urjaman/dasholedsw/mfont8x8.c

#include <stdint.h>
#include <avr/pgmspace.h>

const uint8_t PROGMEM my_font[224][8] = {
	{ 0x00, 0x00, 0x00, 0x00, 0x00, 0x00, 0x00, 0x00 },
	{ 0x00, 0x00, 0x00, 0x7A, 0x00, 0x00, 0x00, 0x00 },
	{ 0x00, 0x00, 0x60, 0x00, 0x00, 0x60, 0x00, 0x00 },
	{ 0x00, 0x24, 0x7E, 0x24, 0x24, 0x7E, 0x24, 0x00 },
	{ 0x00, 0x00, 0x3A, 0x2A, 0x7F, 0x2A, 0x2E, 0x00 },
	{ 0x00, 0x62, 0x64, 0x08, 0x10, 0x26, 0x46, 0x00 },
	{ 0x00, 0x04, 0x2A, 0x52, 0x2A, 0x04, 0x0A, 0x00 },
	{ 0x00, 0x00, 0x00, 0x00, 0x60, 0x00, 0x00, 0x00 },
	{ 0x00, 0x00, 0x00, 0x00, 0x3C, 0x42, 0x00, 0x00 },
	{ 0x00, 0x00, 0x42, 0x3C, 0x00, 0x00, 0x00, 0x00 },
	{ 0x00, 0x00, 0x08, 0x2A, 0x1C, 0x2A, 0x08, 0x00 },
	{ 0x00, 0x00, 0x08, 0x08, 0x3E, 0x08, 0x08, 0x00 },
	{ 0x00, 0x00, 0x00, 0x01, 0x06, 0x00, 0x00, 0x00 },
	{ 0x00, 0x00, 0x08, 0x08, 0x08, 0x08, 0x08, 0x00 },
	{ 0x00, 0x00, 0x00, 0x06, 0x06, 0x00, 0x00, 0x00 },
	{ 0x00, 0x00, 0x02, 0x04, 0x08, 0x10, 0x20, 0x00 },
	{ 0x00, 0x3C, 0x46, 0x4A, 0x52, 0x62, 0x3C, 0x00 },
	{ 0x00, 0x00, 0x22, 0x42, 0x7E, 0x02, 0x02, 0x00 },
	{ 0x00, 0x26, 0x4A, 0x4A, 0x4A, 0x4A, 0x32, 0x00 },
	{ 0x00, 0x24, 0x42, 0x42, 0x52, 0x52, 0x2C, 0x00 },
	{ 0x00, 0x0C, 0x14, 0x24, 0x7E, 0x04, 0x04, 0x00 },
	{ 0x00, 0x74, 0x52, 0x52, 0x52, 0x52, 0x4C, 0x00 },
	{ 0x00, 0x3C, 0x52, 0x52, 0x52, 0x52, 0x0C, 0x00 },
	{ 0x00, 0x40, 0x40, 0x46, 0x48, 0x50, 0x60, 0x00 },
	{ 0x00, 0x2C, 0x52, 0x52, 0x52, 0x52, 0x2C, 0x00 },
	{ 0x00, 0x30, 0x4A, 0x4A, 0x4A, 0x4A, 0x3C, 0x00 },
	{ 0x00, 0x00, 0x00, 0x12, 0x00, 0x00, 0x00, 0x00 },
	{ 0x00, 0x00, 0x01, 0x26, 0x00, 0x00, 0x00, 0x00 },
	{ 0x00, 0x00, 0x00, 0x08, 0x14, 0x22, 0x00, 0x00 },
	{ 0x00, 0x00, 0x14, 0x14, 0x14, 0x14, 0x14, 0x00 },
	{ 0x00, 0x00, 0x00, 0x22, 0x14, 0x08, 0x00, 0x00 },
	{ 0x00, 0x20, 0x40, 0x40, 0x4A, 0x50, 0x20, 0x00 },
	{ 0x00, 0x3C, 0x42, 0x5A, 0x6A, 0x5A, 0x38, 0x00 },
	{ 0x00, 0x3E, 0x48, 0x48, 0x48, 0x48, 0x3E, 0x00 },
	{ 0x00, 0x7E, 0x52, 0x52, 0x52, 0x52, 0x2C, 0x00 },
	{ 0x00, 0x3C, 0x42, 0x42, 0x42, 0x42, 0x24, 0x00 },
	{ 0x00, 0x7E, 0x42, 0x42, 0x42, 0x24, 0x18, 0x00 },
	{ 0x00, 0x7E, 0x52, 0x52, 0x52, 0x52, 0x42, 0x00 },
	{ 0x00, 0x7E, 0x50, 0x50, 0x50, 0x50, 0x40, 0x00 },
	{ 0x00, 0x3C, 0x42, 0x42, 0x4A, 0x4A, 0x2C, 0x00 },
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
};
