urjaman/dasholedsw/lcd.c

#include "main.h"
#include <stdbool.h>
#include <stdint.h>
#include <stdio.h>
#include <avr/io.h>
#include <util/delay.h>

#include "lcd.h"

static uint8_t lcdx, lcdy;

void
lcd_init(void)
{
	dp_init();
}

void lcd_gotoxy(uint8_t x, uint8_t y)
{
	if (y>=LCD_MAXY) y=0;
	if (x>=LCD_MAXX) x=0;
	lcdy = y;
	lcdx = (x*8);
}

void lcd_gotoxy_dw(uint8_t x, uint8_t y)
{
	if (y>=LCD_MAXY) y=0;
	if (x>=LCD_DW_MAXX) x=0;
	lcdy = y;
	lcdx = x;
}


void lcd_clear(void)
{
	dp_clear_block(0, 0, LCDWIDTH, LCDHEIGHT/8);
}

static void lcd_clear_dw_dh(uint8_t w, uint8_t h)
{
	if ((lcdx+w)>LCDWIDTH) {
		w = LCDWIDTH - lcdx;
	}
	dp_clear_block(lcdx, lcdy, w, h);
	lcdx += w;
}

void lcd_clear_dw(uint8_t w)
{
	lcd_clear_dw_dh(w, 1);
}

void lcd_clear_big_dw(uint8_t w)
{
	lcd_clear_dw_dh(w, 2);
}

void lcd_clear_dbig_dw(uint8_t w)
{
	lcd_clear_dw_dh(w, 4);
}

static void lcd_clear_eol_dh(uint8_t h)
{
	dp_clear_block(lcdx, lcdy, LCDWIDTH - lcdx, h);
	lcdx = 0;
	lcdy += h;
}

void lcd_clear_eol(void)
{
	lcd_clear_eol_dh(1);
}

void lcd_clear_big_eol(void)
{
	lcd_clear_eol_dh(2);
}

void lcd_clear_dbig_eol(void)
{
	lcd_clear_eol_dh(4);
}

void lcd_clear_eos(void)
{
	while (lcdy < LCD_MAXY) lcd_clear_eol();
	lcdy = 0;
}

void lcd_write_dwb(uint8_t *buf, uint8_t w)
{
	if ((lcdx+w)>LCDWIDTH) {
		w = LCDWIDTH - lcdx;
	}
	dp_write_block(buf, lcdx, lcdy, w, 1);
	lcdx += w;
}

#include "mfont8x8.c"

// Some data for dynamic width mode with this font.
#include "font-dyn-meta.c"

static PGM_P get_block(uint8_t *w, unsigned char c, uint8_t dw)
{
	PGM_P block;
	if (c < 0x20) c = 0x20;
	block = (const char*)&(my_font[c-0x20][0]);
	*w = 8;
	if (dw) {
		uint8_t font_meta_b = pgm_read_byte(&(font_metadata[c-0x20]));
		block += XOFF(font_meta_b);
		*w = DW(font_meta_b);
	}
	return block;
}

uint8_t lcd_get_strbuf(uint8_t *b, const unsigned char*str, uint8_t dw)
{
	uint8_t o=0,w;
	PGM_P block;
	while (*str) {
		block = get_block(&w, *str++, dw);
		memcpy_P(b+o, block, w);
		o += w;
	}
	return o;
}

static void lcd_putchar_(unsigned char c, uint8_t dw)
{

	uint8_t w;
	PGM_P block = get_block(&w, c, dw);
	if ((lcdx+w)>LCDWIDTH) {
		w = LCDWIDTH - lcdx;
	}
	dp_write_block_P(block, lcdx, lcdy, w, 1);
	lcdx += w;
}



static void lcd_putchar_big(unsigned char c)
{
	uint8_t buf[32];

	uint8_t w;
	PGM_P block = get_block(&w, c, 1);

	if ((lcdx+(w*2))>LCDWIDTH) {
		w = (LCDWIDTH - lcdx)/2;
	}
	for (int i=0; i<w; i++) {
		uint8_t d = pgm_read_byte(block);
		block++;
		uint8_t hi = 0;
		uint8_t lo = 0;
		for (int i=0; i<4; i++) {
			hi = hi >> 2;
			lo = lo >> 2;
			if (d & _BV(4+i)) hi |= 0xC0;
			if (d & _BV(i)) lo |= 0xC0;
		}
		buf[i*2] = hi;
		buf[i*2+1] = hi;
		buf[(w+i)*2] = lo;
		buf[(w+i)*2+1] = lo;
	}
	dp_write_block(buf, lcdx, lcdy, w*2, 2);
	lcdx += w*2;
}


static void lcd_putchar_dbig(unsigned char c)
{
	uint8_t buf[128];

	uint8_t w;
	PGM_P block = get_block(&w, c, 1);
	if ((lcdx+(w*4))>LCDWIDTH) {
		w = (LCDWIDTH - lcdx)/2;
	}
	for (uint8_t i=0; i<w; i++) {
		uint8_t dat = pgm_read_byte(block);
		block++;
		uint8_t a = 0;
		uint8_t b = 0;
		uint8_t c = 0;
		uint8_t d = 0;
		for (uint8_t n=0; n<2; n++) {
			a = a >> 4;
			b = b >> 4;
			c = c >> 4;
			d = d >> 4;
			if (dat & _BV(6+n)) a |= 0xF0;
			if (dat & _BV(4+n)) b |= 0xF0;
			if (dat & _BV(2+n)) c |= 0xF0;
			if (dat & _BV(n))   d |= 0xF0;
		}
		memset(buf+i*4, a, 4);
		memset(buf+(w+i)*4, b, 4);
		memset(buf+(2*w+i)*4, c, 4);
		memset(buf+(3*w+i)*4, d, 4);
	}
	dp_write_block(buf, lcdx, lcdy, w*4, 4);
	lcdx += w*4;
}

static uint8_t lcd_dw_charw(uint8_t c)
{
	if (c < 0x20) c = 0x20;
	uint8_t font_meta_b = pgm_read_byte(&(font_metadata[c-0x20]));
	return DW(font_meta_b);
}


uint8_t lcd_strwidth(const unsigned char * str)
{
	uint8_t w = 0;
	do {
		if (*str) w += lcd_dw_charw(*str);
		else return w;
		str++;
	} while(1);
}

uint8_t lcd_strwidth_P(PGM_P str)
{
	uint8_t w = 0;
	do {
		uint8_t c = pgm_read_byte(str);
		if (c) w += lcd_dw_charw(c);
		else return w;
		str++;
	} while(1);
}

/* big = 2x small, but dont tell the user ;) */
uint8_t lcd_strwidth_big(const unsigned char * str)
{
	return lcd_strwidth(str)*2;
}

uint8_t lcd_strwidth_big_P(PGM_P str)
{
	return lcd_strwidth_P(str)*2;
}

/* dbig = 4x small, but dont tell the user ;) */
uint8_t lcd_strwidth_dbig(const unsigned char * str)
{
	return lcd_strwidth(str)*4;
}

uint8_t lcd_strwidth_dbig_P(PGM_P str)
{
	return lcd_strwidth_P(str)*4;
}

void lcd_putchar(unsigned char c)
{
	lcd_putchar_(c,0);
}

void lcd_puts(const unsigned char * str)
{
	do {
		if (*str) lcd_putchar_(*str, 0);
		else return;
		str++;
	} while(1);
}

void lcd_puts_P(PGM_P str)
{
	do {
		uint8_t c = pgm_read_byte(str);
		if (c) lcd_putchar_(c, 0);
		else return;
		str++;
	} while (1);
}

void lcd_puts_dw(const unsigned char * str)
{
start:
	if (*str) lcd_putchar_(*str, 1);
	else return;
	str++;
	goto start;
}

void lcd_puts_dw_P(PGM_P str)
{
	unsigned char c;
start:
	c = pgm_read_byte(str);
	if (c) lcd_putchar_(c, 1);
	else return;
	str++;
	goto start;
}


void lcd_puts_big_P(PGM_P str)
{
	unsigned char c;
start:
	c = pgm_read_byte(str);
	if (c) lcd_putchar_big(c);
	else return;
	str++;
	goto start;
}

void lcd_puts_big(const unsigned char * str)
{
start:
	if (*str) lcd_putchar_big(*str);
	else return;
	str++;
	goto start;
}

void lcd_puts_dbig_P(PGM_P str)
{
	unsigned char c;
start:
	c = pgm_read_byte(str);
	if (c) lcd_putchar_dbig(c);
	else return;
	str++;
	goto start;
}

void lcd_puts_dbig(const unsigned char * str)
{
start:
	if (*str) lcd_putchar_dbig(*str);
	else return;
	str++;
	goto start;
}

/* Fill the screen with one character. */
void lcd_huge_char(uint8_t c)
{
	uint8_t dummy;
	PGM_P block = get_block(&dummy, c, 0);
	uint8_t buf[64];
	lcd_gotoxy_dw(0,0);
	uint8_t extra = (LCDWIDTH - 64) / 2;
	for (uint8_t b=0x80; b; b = b >> 1) {
		lcd_clear_dw(extra);
		for (uint8_t n=0; n<8; n++) {
			if (pgm_read_byte(block+n) & b) {
				memset(buf+n*8,0xFF,8);
			} else {
				memset(buf+n*8,0,8);
			}
		}
		lcd_write_dwb(buf, 64);
		lcd_clear_eol();
	}
	lcd_clear_eos();
}
