urjaman/dasholedsw/ssd1331.h

#pragma once
/***************************************************
  This is a library for the 0.96" 16-bit Color OLED with SSD1331 driver chip

  Pick one up today in the adafruit shop!
  ------> http://www.adafruit.com/products/684

  These displays use SPI to communicate, 4 or 5 pins are required to
  interface
  Adafruit invests time and resources providing this open source code,
  please support Adafruit and open-source hardware by purchasing
  products from Adafruit!

  Written by Limor Fried/Ladyada for Adafruit Industries.
  BSD license, all text above must be included in any redistribution
 ****************************************************/
/* This has been modified by Urja Rannikko <urjaman@gmail.com> */

// Select one of these defines to set the pixel color order
#define SSD1331_COLORORDER_RGB
// #define SSD1331_COLORORDER_BGR

// Timing Delays
#define SSD1331_DELAYS_HWFILL		(3)
#define SSD1331_DELAYS_HWLINE       (1)

// SSD1331 Commands
#define SSD1331_CMD_DRAWLINE 		0x21
#define SSD1331_CMD_DRAWRECT 		0x22
#define SSD1331_CMD_FILL 		0x26
#define SSD1331_CMD_SETCOLUMN 		0x15
#define SSD1331_CMD_SETROW    		0x75
#define SSD1331_CMD_CONTRASTA 		0x81
#define SSD1331_CMD_CONTRASTB 		0x82
#define SSD1331_CMD_CONTRASTC		0x83
#define SSD1331_CMD_MASTERCURRENT 	0x87
#define SSD1331_CMD_SETREMAP 		0xA0
#define SSD1331_CMD_STARTLINE 		0xA1
#define SSD1331_CMD_DISPLAYOFFSET 	0xA2
#define SSD1331_CMD_NORMALDISPLAY 	0xA4
#define SSD1331_CMD_DISPLAYALLON  	0xA5
#define SSD1331_CMD_DISPLAYALLOFF 	0xA6
#define SSD1331_CMD_INVERTDISPLAY 	0xA7
#define SSD1331_CMD_SETMULTIPLEX  	0xA8
#define SSD1331_CMD_SETMASTER 		0xAD
#define SSD1331_CMD_DISPLAYOFF 		0xAE
#define SSD1331_CMD_DISPLAYON     	0xAF
#define SSD1331_CMD_POWERMODE 		0xB0
#define SSD1331_CMD_PRECHARGE 		0xB1
#define SSD1331_CMD_CLOCKDIV 		0xB3
#define SSD1331_CMD_PRECHARGEA 		0x8A
#define SSD1331_CMD_PRECHARGEB 		0x8B
#define SSD1331_CMD_PRECHARGEC 		0x8C
#define SSD1331_CMD_PRECHARGELEVEL 	0xBB
#define SSD1331_CMD_VCOMH		0xBE


/* My more and more generic "LCD" API. */

#define LCDWIDTH 96
#define LCDHEIGHT 64

#define LCD_CHARW 8

/* dp = generic display */

void dp_write_block_P(const PGM_P buffer, uint8_t x, uint8_t y, uint8_t w, uint8_t h);
void dp_write_block(const uint8_t *buffer, uint8_t x, uint8_t y, uint8_t w, uint8_t h);
void dp_clear_block(uint8_t x, uint8_t y, uint8_t w, uint8_t h);

#define DP_HAS_COLOR

typedef uint16_t color_t;

#define dp_get_color(r,g,b) ((((r)<<8)&0xF800) | (((g)<<3)&0x07E0) | ((b)>>3))
#define rgb(r,g,b) dp_get_color(r,g,b)

//uint16_t dp_get_color(uint8_t r, uint8_t g, uint8_t b);
void dp_set_fg_bg(color_t fg, color_t bg);

#define DP_HAS_BL
void dp_set_bl(uint8_t bl);

void dp_init(void);

uint8_t dp_draw_tgif(const void *tgif, uint8_t x, uint8_t y, uint8_t w, uint8_t h);
