urjaman/dasholedsw/uart.c

#include "main.h"
#include "lib.h"
#include "uart.h"
#include "console.h"
#include "timer.h"
#include "cron.h"
#ifdef ENABLE_UARTMODULE

// UART MODULE START
typedef unsigned char urxbufoff_t;
#define UART_BUFLEN 16
unsigned char volatile uart_rcvbuf[UART_BUFLEN];
urxbufoff_t volatile uart_rcvwptr;
urxbufoff_t volatile uart_rcvrptr;


ISR(USART_RX_vect)
{
	urxbufoff_t reg = uart_rcvwptr;
	uart_rcvbuf[reg++] = UDR0;
	if(reg==UART_BUFLEN) reg = 0;
	uart_rcvwptr = reg;
}


ISR(USART_UDRE_vect)
{
	utxbufoff_t reg = uart_sndrptr;
	if (uart_sndwptr != reg) {
		UDR0 = uart_sndbuf[reg++];
		if (reg==UARTTX_BUFLEN) reg = 0;
		uart_sndrptr = reg;
		return;
	} else {
		UCSR0B &= ~_BV(5);
		return;
	}
}


uint8_t uart_isdata(void)
{
	if (uart_rcvwptr != uart_rcvrptr) { return 1; }
	else { return 0; }
}

uint8_t uart_recv(void)
{
	urxbufoff_t reg;
	unsigned char val;
	while (!uart_isdata()); // when there's nothing to do, one might idle...
	reg = uart_rcvrptr;
	val = uart_rcvbuf[reg++];
	if(reg==UART_BUFLEN) reg = 0;
	uart_rcvrptr = reg;
	return val;
}

void uart_send(uint8_t val)
{
	utxbufoff_t reg;
	while (uart_sndwptr+1==uart_sndrptr || (uart_sndwptr+1==UARTTX_BUFLEN
	                                        && !uart_sndrptr)); // wait for space in buf
	cli();
	reg = uart_sndwptr;
	UCSR0B |= _BV(5); // make sure the transmit int is on
	uart_sndbuf[reg++] = val; // add byte to the transmit queue
	if(reg==UARTTX_BUFLEN) reg = 0;
	uart_sndwptr = reg;
	sei();
}

void uart_init(void)
{
	cli();

#include <util/setbaud.h>
// Assuming uart.h defines BAUD
	uart_rcvwptr = 0;
	uart_rcvrptr = 0;
	uart_sndwptr = 0;
	uart_sndrptr = 0;
	UBRR0H = UBRRH_VALUE;
	UBRR0L = UBRRL_VALUE;
	UCSR0C = 0x06; // Async USART,No Parity,1 stop bit, 8 bit chars
	UCSR0A &= 0xFC;
#if USE_2X
	UCSR0A |= (1 << U2X0);
#endif
	UCSR0B = 0xB8; // RX complete interrupt enable, UDRE int en, Receiver & Transmitter enable
	sei();
}

void uart_wait_txdone(void)
{
	while (uart_sndwptr != uart_sndrptr);
}

#else
void uart_wait_txdone(void) { }
void uart_init(void) { }
void uart_send(uint8_t val) { val = val; }
uint8_t uart_recv(void) { return 0; }
uint8_t uart_isdata(void) { return 0; }
#endif
