urjaman/dasholedsw/adc.h

/* This isnt really main battery, but power input voltage. */
#define ADC_CH_MB 4
/* There's no channel dedicated for SB, but I say reuse R10V for that if we use this for relay ctrl
 * application */
#define ADC_CH_SB 3

#define ADC_CH_R10V 3
#define ADC_CH_FUEL 2
#define ADC_CH_TEMP 1
#define ADC_CH_BACKLIGHT 0

uint16_t adc_read_ch(uint8_t ch);

uint16_t adc_read_mb(void);
uint16_t adc_read_sb(void);
int16_t adc_read_diff(void);
uint16_t adc_read_minv(uint8_t ch);
uint16_t adc_read_maxv(uint8_t ch);

void adc_print_v(unsigned char* buf, uint16_t v);
void adc_init(void);
void adc_run(void);
uint16_t adc_to_dV(uint16_t v);
uint16_t adc_from_dV(uint16_t v);
void adc_print_dV(unsigned char* buf, uint16_t v);

// LOTS of places need to be changed if ADC_MUX_CNT!=2.
#define ADC_MUX_CNT 5
extern int16_t adc_calibration_diff[ADC_MUX_CNT];
