urjaman/dasholedsw/buttons.h

void buttons_init(void);
uint8_t buttons_get(void);
uint8_t buttons_get_v(void);
uint8_t buttons_hw_count(void);


#define BUTTON_NEXT 8
#define BUTTON_PREV 4
#define BUTTON_OK 2
#define BUTTON_CANCEL 1
